gupid/Spacemouse_DIY_project/Spacemouse_develop/3Dmouse_keyboard/Profile/hid_composite_service.c

/********************************** (C) COPYRIGHT *******************************
 * File Name          : hidkbdservice.c
 * Author             : WCH
 * Version            : V1.0
 * Date               : 2018/12/10
 * Description        : 键盘服务
 *********************************************************************************
 * Copyright (c) 2021 Nanjing Qinheng Microelectronics Co., Ltd.
 * Attention: This software (modified or not) and binary are used for 
 * microcontroller manufactured by Nanjing Qinheng Microelectronics.
 *******************************************************************************/

/*********************************************************************
 * INCLUDES
 */
#include "CONFIG.h"
#include "hid_composite_service.h"
#include "hiddev.h"
#include "battservice.h"

/*********************************************************************
 * MACROS
 */

/*********************************************************************
 * CONSTANTS
 */

/*********************************************************************
 * TYPEDEFS
 */

/*********************************************************************
 * GLOBAL VARIABLES
 */
// HID service
const uint8_t hidServUUID[ATT_BT_UUID_SIZE] = {
    LO_UINT16(HID_SERV_UUID), HI_UINT16(HID_SERV_UUID)};

// HID Boot Keyboard Input Report characteristic
const uint8_t hidBootKeyInputUUID[ATT_BT_UUID_SIZE] = {
    LO_UINT16(BOOT_KEY_INPUT_UUID), HI_UINT16(BOOT_KEY_INPUT_UUID)};

// HID Boot Keyboard Output Report characteristic
const uint8_t hidBootKeyOutputUUID[ATT_BT_UUID_SIZE] = {
    LO_UINT16(BOOT_KEY_OUTPUT_UUID), HI_UINT16(BOOT_KEY_OUTPUT_UUID)};

// HID Information characteristic
const uint8_t hidInfoUUID[ATT_BT_UUID_SIZE] = {
    LO_UINT16(HID_INFORMATION_UUID), HI_UINT16(HID_INFORMATION_UUID)};

// HID Report Map characteristic
const uint8_t hidReportMapUUID[ATT_BT_UUID_SIZE] = {
    LO_UINT16(REPORT_MAP_UUID), HI_UINT16(REPORT_MAP_UUID)};

// HID Control Point characteristic
const uint8_t hidControlPointUUID[ATT_BT_UUID_SIZE] = {
    LO_UINT16(HID_CTRL_PT_UUID), HI_UINT16(HID_CTRL_PT_UUID)};

// HID Report characteristic
const uint8_t hidReportUUID[ATT_BT_UUID_SIZE] = {
    LO_UINT16(REPORT_UUID), HI_UINT16(REPORT_UUID)};

// HID Protocol Mode characteristic
const uint8_t hidProtocolModeUUID[ATT_BT_UUID_SIZE] = {
    LO_UINT16(PROTOCOL_MODE_UUID), HI_UINT16(PROTOCOL_MODE_UUID)};

/*********************************************************************
 * EXTERNAL VARIABLES
 */

/*********************************************************************
 * EXTERNAL FUNCTIONS
 */

/*********************************************************************
 * LOCAL VARIABLES
 */

// HID Information characteristic value
static const uint8_t hidInfo[HID_INFORMATION_LEN] = {
    LO_UINT16(0x0111), HI_UINT16(0x0111), // bcdHID (USB HID version)
    0x00,                                 // bCountryCode
    HID_FEATURE_FLAGS                     // Flags
};

// hid_composite_service.c

// HID Report Map characteristic value (Corrected and Aligned with USB Version)
static const uint8_t hidReportMap[] = {
    // --- TLC 1: SpaceMouse ---
    0x05, 0x01,       // Usage Page (Generic Desktop)
    0x09, 0x08,       // Usage (Multi-Axis Controller)
    0xA1, 0x01,       // Collection (Application)
        // 报告ID 1: 平移
        0x85, 0x01,       //   Report ID (1)
        0x09, 0x30,       //   Usage (X)
        0x09, 0x31,       //   Usage (Y)
        0x09, 0x32,       //   Usage (Z)
        0x16, 0xA2, 0xFE, //   Logical Minimum (-350)
        0x26, 0x5E, 0x01, //   Logical Maximum (350)
        0x75, 0x10,       //   Report Size (16)
        0x95, 0x03,       //   Report Count (3)
        0x81, 0x02,       //   Input (Data, Var, Abs)
        // 报告ID 2: 旋转
        0x85, 0x02,       //   Report ID (2)
        0x09, 0x33,       //   Usage (Rx)
        0x09, 0x34,       //   Usage (Ry)
        0x09, 0x35,       //   Usage (Rz)
        0x16, 0xA2, 0xFE, //   Logical Minimum (-350)
        0x26, 0x5E, 0x01, //   Logical Maximum (350)
        0x75, 0x10,       //   Report Size (16)
        0x95, 0x03,       //   Report Count (3)
        0x81, 0x02,       //   Input (Data, Var, Abs)
        // 报告ID 3: 按键
        0x85, 0x03,       //   Report ID (3)
        0x05, 0x09,       //   Usage Page (Button)
        0x19, 0x01,       //   Usage Minimum (Button 1)
        0x29, 0x20,       //   Usage Maximum (Button 32)
        0x15, 0x00,       //   Logical Minimum (0)
        0x25, 0x01,       //   Logical Maximum (1)
        0x75, 0x01,       //   Report Size (1)
        0x95, 0x20,       //   Report Count (32)
        0x81, 0x02,       //   Input (Data, Var, Abs)
        // 报告ID 4: LED
        0x85, 0x04,       //   Report ID (4)
        0x05, 0x08,       //   Usage Page (LEDs)
        0x09, 0x4B,       //   Usage (Generic Indicator)
        0x15, 0x00,       //   Logical Minimum (0)
        0x25, 0x01,       //   Logical Maximum (1)
        0x75, 0x01,       //   Report Size (1)
        0x95, 0x01,       //   Report Count (1)
        0x91, 0x02,       //   Output (Data, Var, Abs)
        0x75, 0x07,       //   Report Size (7) - Padding
        0x95, 0x01,       //   Report Count (1)
        0x91, 0x03,       //   Output (Constant)
    0xC0,             // End Collection (SpaceMouse)

    // --- TLC 2: Keyboard ---
    0x05, 0x01,       // Usage Page (Generic Desktop)
    0x09, 0x06,       // Usage (Keyboard)
    0xA1, 0x01,       // Collection (Application)
        // 报告ID 5: 键盘输入/输出
        0x85, 0x05,       //   Report ID (5)
        // Modifier keys (Input)
        0x05, 0x07,       //   Usage Page (Key Codes)
        0x19, 0xE0,       //   Usage Minimum (LeftControl)
        0x29, 0xE7,       //   Usage Maximum (RightGUI)
        0x15, 0x00,       //   Logical Minimum (0)
        0x25, 0x01,       //   Logical Maximum (1)
        0x75, 0x01,       //   Report Size (1)
        0x95, 0x08,       //   Report Count (8)
        0x81, 0x02,       //   Input (Data, Var, Abs)
        // Reserved byte (Input)
        0x95, 0x01,       //   Report Count (1)
        0x75, 0x08,       //   Report Size (8)
        0x81, 0x01,       //   Input (Constant)
        // Key array (Input)
        0x95, 0x06,       //   Report Count (6)
        0x75, 0x08,       //   Report Size (8)
        0x15, 0x00,       //   Logical Minimum (0)
        0x25, 0x65,       //   Logical Maximum (101)
        0x05, 0x07,       //   Usage Page (Key Codes)
        0x19, 0x00,       //   Usage Minimum (Reserved)
        0x29, 0x65,       //   Usage Maximum (Keyboard Application)
        0x81, 0x00,       //   Input (Data, Array)
        // LED (Output)
        0x05, 0x08,       //   Usage Page (LEDs)
        0x19, 0x01,       //   Usage Minimum (Num Lock)
        0x29, 0x05,       //   Usage Maximum (Kana)
        0x95, 0x05,       //   Report Count (5)
        0x75, 0x01,       //   Report Size (1)
        0x91, 0x02,       //   Output (Data, Var, Abs)
        // LED padding (Output)
        0x95, 0x01,       //   Report Count (1)
        0x75, 0x03,       //   Report Size (3)
        0x91, 0x03,       //   Output (Constant)
    0xC0,             // End Collection (Keyboard)

    // --- TLC 3: Feature Report (可以保持独立或合并) ---
    // 这个报告比较特殊，可以单独存在
    0x05, 0x01,       // Usage Page (Generic Desktop)
    0x09, 0x00,       // Usage (Undefined)
    0xA1, 0x01,       // Collection (Application)
        // 报告ID 6: Feature 报告
        0x85, 0x06,       // Report ID (6)
        0x09, 0x01,       // Usage (Pointer)
        0x15, 0x00,       // Logical Minimum (0)
        0x26, 0xFF, 0x00, // Logical Maximum (255)
        0x75, 0x08,       // Report Size (8)
        0x95, 0x01,       // Report Count (1)
        0xB1, 0x02,       // Feature (Data,Var,Abs)
    0xC0              // End Collection
};

// HID report map length
uint16_t hidReportMapLen = sizeof(hidReportMap);

// HID report mapping table
static hidRptMap_t hidRptMap[HID_NUM_REPORTS];

/*********************************************************************
 * Profile Attributes - variables
 */

// HID Service attribute
static const gattAttrType_t hidService = {ATT_BT_UUID_SIZE, hidServUUID};

// Include attribute (Battery service)
static uint16_t include = GATT_INVALID_HANDLE;

// HID Information characteristic
static uint8_t hidInfoProps = GATT_PROP_READ;

// HID Report Map characteristic
static uint8_t hidReportMapProps = GATT_PROP_READ;

// HID External Report Reference Descriptor
static uint8_t hidExtReportRefDesc[ATT_BT_UUID_SIZE] =
    {LO_UINT16(BATT_LEVEL_UUID), HI_UINT16(BATT_LEVEL_UUID)};

// HID Control Point characteristic
static uint8_t hidControlPointProps = GATT_PROP_WRITE_NO_RSP;
static uint8_t hidControlPoint;

// HID Protocol Mode characteristic
static uint8_t hidProtocolModeProps = GATT_PROP_READ | GATT_PROP_WRITE_NO_RSP;
uint8_t        hidProtocolMode = HID_PROTOCOL_MODE_REPORT;

// HID Report characteristic, key input
static uint8_t       hidReportKeyInProps = GATT_PROP_READ | GATT_PROP_NOTIFY;
static uint8_t       hidReportKeyIn;
static gattCharCfg_t hidReportKeyInClientCharCfg[GATT_MAX_NUM_CONN];

// HID Report Reference characteristic descriptor, key input
static uint8_t hidReportRefKeyIn[HID_REPORT_REF_LEN] =
    {HID_RPT_ID_KEY_IN, HID_REPORT_TYPE_INPUT};

// HID Report characteristic, LED output
static uint8_t hidReportLedOutProps = GATT_PROP_READ | GATT_PROP_WRITE | GATT_PROP_WRITE_NO_RSP;
static uint8_t hidReportLedOut;

// HID Report Reference characteristic descriptor, LED output
static uint8_t hidReportRefLedOut[HID_REPORT_REF_LEN] =
    {HID_RPT_ID_LED_OUT, HID_REPORT_TYPE_OUTPUT};

// HID Boot Keyboard Input Report
static uint8_t       hidReportBootKeyInProps = GATT_PROP_READ | GATT_PROP_NOTIFY;
static uint8_t       hidReportBootKeyIn;
static gattCharCfg_t hidReportBootKeyInClientCharCfg[GATT_MAX_NUM_CONN];

// HID Boot Keyboard Output Report
static uint8_t hidReportBootKeyOutProps = GATT_PROP_READ | GATT_PROP_WRITE | GATT_PROP_WRITE_NO_RSP;
static uint8_t hidReportBootKeyOut;

// Feature Report
static uint8_t hidReportFeatureProps = GATT_PROP_READ | GATT_PROP_WRITE;
static uint8_t hidReportFeature;

// HID Report Reference characteristic descriptor, Feature
static uint8_t hidReportRefFeature[HID_REPORT_REF_LEN] =
    {HID_RPT_ID_FEATURE, HID_REPORT_TYPE_FEATURE};

// ---SpaceMouse平移报告 (ID: 2)---
static uint8_t       hidReportSpaceTransInProps = GATT_PROP_READ | GATT_PROP_NOTIFY;
static uint8_t       hidReportSpaceTransIn;
static gattCharCfg_t hidReportSpaceTransInClientCharCfg[GATT_MAX_NUM_CONN];
// 定义平移报告ID为2，类型为输入
static uint8_t hidReportRefSpaceTransIn[HID_REPORT_REF_LEN] = { HID_RPT_ID_SPACE_TRANS_IN, HID_REPORT_TYPE_INPUT };

// ---SpaceMouse旋转报告 (ID: 3)---
static uint8_t       hidReportSpaceRotInProps = GATT_PROP_READ | GATT_PROP_NOTIFY;
static uint8_t       hidReportSpaceRotIn;
static gattCharCfg_t hidReportSpaceRotInClientCharCfg[GATT_MAX_NUM_CONN];
// 定义旋转报告ID为3，类型为输入
static uint8_t hidReportRefSpaceRotIn[HID_REPORT_REF_LEN] = { HID_RPT_ID_SPACE_ROT_IN, HID_REPORT_TYPE_INPUT };

// --- SpaceMouse按键报告 (ID: 4) ---
static uint8_t       hidReportSpaceBtnInProps = GATT_PROP_READ | GATT_PROP_NOTIFY;
static uint8_t       hidReportSpaceBtnIn;
static gattCharCfg_t hidReportSpaceBtnInClientCharCfg[GATT_MAX_NUM_CONN];
// 定义按键报告ID为4，类型为输入
static uint8_t hidReportRefSpaceBtnIn[HID_REPORT_REF_LEN] = { HID_RPT_ID_SPACE_BTN_IN, HID_REPORT_TYPE_INPUT };

// --- SpaceMouse LED输出报告 (ID: 5) ---
static uint8_t hidReportSpaceLedOutProps = GATT_PROP_READ | GATT_PROP_WRITE | GATT_PROP_WRITE_NO_RSP;
static uint8_t hidReportSpaceLedOut;
// 定义LED报告ID为5，类型为输出
static uint8_t hidReportRefSpaceLedOut[HID_REPORT_REF_LEN] = { HID_RPT_ID_SPACE_LED_OUT, HID_REPORT_TYPE_OUTPUT };
/*********************************************************************
 * Profile Attributes - Table
 */

static gattAttribute_t hidAttrTbl[] = {
    // HID Service
    {
        {ATT_BT_UUID_SIZE, primaryServiceUUID}, /* type */
        GATT_PERMIT_READ,                       /* permissions */
        0,                                      /* handle */
        (uint8_t *)&hidService                  /* pValue */
    },

    // Included service (battery)
    {
        {ATT_BT_UUID_SIZE, includeUUID},
        GATT_PERMIT_READ,
        0,
        (uint8_t *)&include},

    // HID Information characteristic declaration
    {
        {ATT_BT_UUID_SIZE, characterUUID},
        GATT_PERMIT_READ,
        0,
        &hidInfoProps},

    // HID Information characteristic
    {
        {ATT_BT_UUID_SIZE, hidInfoUUID},
        GATT_PERMIT_ENCRYPT_READ,
        0,
        (uint8_t *)hidInfo},

    // HID Control Point characteristic declaration
    {
        {ATT_BT_UUID_SIZE, characterUUID},
        GATT_PERMIT_READ,
        0,
        &hidControlPointProps},

    // HID Control Point characteristic
    {
        {ATT_BT_UUID_SIZE, hidControlPointUUID},
        GATT_PERMIT_ENCRYPT_WRITE,
        0,
        &hidControlPoint},

    // HID Protocol Mode characteristic declaration
    {
        {ATT_BT_UUID_SIZE, characterUUID},
        GATT_PERMIT_READ,
        0,
        &hidProtocolModeProps},

    // HID Protocol Mode characteristic
    {
        {ATT_BT_UUID_SIZE, hidProtocolModeUUID},
        GATT_PERMIT_ENCRYPT_READ | GATT_PERMIT_ENCRYPT_WRITE,
        0,
        &hidProtocolMode},

    // HID Report Map characteristic declaration
    {
        {ATT_BT_UUID_SIZE, characterUUID},
        GATT_PERMIT_READ,
        0,
        &hidReportMapProps},

    // HID Report Map characteristic
    {
        {ATT_BT_UUID_SIZE, hidReportMapUUID},
        GATT_PERMIT_ENCRYPT_READ,
        0,
        (uint8_t *)hidReportMap},

    // HID External Report Reference Descriptor
    {
        {ATT_BT_UUID_SIZE, extReportRefUUID},
        GATT_PERMIT_READ,
        0,
        hidExtReportRefDesc

    },

    // HID Report characteristic, key input declaration
    {
        {ATT_BT_UUID_SIZE, characterUUID},
        GATT_PERMIT_READ,
        0,
        &hidReportKeyInProps},

    // HID Report characteristic, key input
    {
        {ATT_BT_UUID_SIZE, hidReportUUID},
        GATT_PERMIT_ENCRYPT_READ,
        0,
        &hidReportKeyIn},

    // HID Report characteristic client characteristic configuration
    {
        {ATT_BT_UUID_SIZE, clientCharCfgUUID},
        GATT_PERMIT_READ | GATT_PERMIT_ENCRYPT_WRITE,
        0,
        (uint8_t *)&hidReportKeyInClientCharCfg},

    // HID Report Reference characteristic descriptor, key input
    {
        {ATT_BT_UUID_SIZE, reportRefUUID},
        GATT_PERMIT_READ,
        0,
        hidReportRefKeyIn},

    // HID Report characteristic, LED output declaration
    {
        {ATT_BT_UUID_SIZE, characterUUID},
        GATT_PERMIT_READ,
        0,
        &hidReportLedOutProps},

    // HID Report characteristic, LED output
    {
        {ATT_BT_UUID_SIZE, hidReportUUID},
        GATT_PERMIT_ENCRYPT_READ | GATT_PERMIT_ENCRYPT_WRITE,
        0,
        &hidReportLedOut},
        
    // HID Report Reference characteristic descriptor, LED output
    {
        {ATT_BT_UUID_SIZE, reportRefUUID},
        GATT_PERMIT_READ,
        0,
        hidReportRefLedOut
    },

    // --- HID Report characteristic, SpaceMouse translation input declaration ---
    {
        {ATT_BT_UUID_SIZE, characterUUID},
        GATT_PERMIT_READ,
        0,
        &hidReportSpaceTransInProps
    },

    // --- HID Report characteristic, SpaceMouse translation input ---
    {
        {ATT_BT_UUID_SIZE, hidReportUUID},
        GATT_PERMIT_ENCRYPT_READ,
        0,
        &hidReportSpaceTransIn
    },

    // --- HID Report characteristic client characteristic configuration (CCCD) ---
    {
        {ATT_BT_UUID_SIZE, clientCharCfgUUID},
        GATT_PERMIT_READ | GATT_PERMIT_ENCRYPT_WRITE,
        0,
        (uint8_t *)&hidReportSpaceTransInClientCharCfg
    },

    // --- HID Report Reference characteristic descriptor, SpaceMouse translation input ---
    {
        {ATT_BT_UUID_SIZE, reportRefUUID},
        GATT_PERMIT_READ,
        0,
        hidReportRefSpaceTransIn
    },

    // --- HID Report characteristic, SpaceMouse rotation input declaration ---
    {
        {ATT_BT_UUID_SIZE, characterUUID},
        GATT_PERMIT_READ,
        0,
        &hidReportSpaceRotInProps
    },

    // --- HID Report characteristic, SpaceMouse rotation input ---
    {
        {ATT_BT_UUID_SIZE, hidReportUUID},
        GATT_PERMIT_ENCRYPT_READ,
        0,
        &hidReportSpaceRotIn
    },

    // --- HID Report characteristic client characteristic configuration (CCCD) ---
    {
        {ATT_BT_UUID_SIZE, clientCharCfgUUID},
        GATT_PERMIT_READ | GATT_PERMIT_ENCRYPT_WRITE,
        0,
        (uint8_t *)&hidReportSpaceRotInClientCharCfg
    },

    // --- HID Report Reference characteristic descriptor, SpaceMouse rotation input ---
    {
        {ATT_BT_UUID_SIZE, reportRefUUID},
        GATT_PERMIT_READ,
        0,
        hidReportRefSpaceRotIn
    },

    // --- [!!] 新增：HID Report characteristic, SpaceMouse button input declaration ---
    {
        {ATT_BT_UUID_SIZE, characterUUID},
        GATT_PERMIT_READ,
        0,
        &hidReportSpaceBtnInProps
    },

    // --- [!!] 新增：HID Report characteristic, SpaceMouse button input ---
    {
        {ATT_BT_UUID_SIZE, hidReportUUID}, // 使用通用报告UUID
        GATT_PERMIT_ENCRYPT_READ,
        0,
        &hidReportSpaceBtnIn
    },

    // --- [!!] 新增：HID Report characteristic client characteristic configuration (CCCD) ---
    {
        {ATT_BT_UUID_SIZE, clientCharCfgUUID},
        GATT_PERMIT_READ | GATT_PERMIT_ENCRYPT_WRITE,
        0,
        (uint8_t *)&hidReportSpaceBtnInClientCharCfg
    },

    // --- [!!] 新增：HID Report Reference characteristic descriptor, SpaceMouse button input ---
    {
        {ATT_BT_UUID_SIZE, reportRefUUID},
        GATT_PERMIT_READ,
        0,
        hidReportRefSpaceBtnIn
    },

    // --- [!!] 新增：HID Report characteristic, SpaceMouse LED output declaration ---
    {
        {ATT_BT_UUID_SIZE, characterUUID},
        GATT_PERMIT_READ,
        0,
        &hidReportSpaceLedOutProps
    },

    // --- [!!] 新增：HID Report characteristic, SpaceMouse LED output ---
    {
        {ATT_BT_UUID_SIZE, hidReportUUID}, // 使用通用报告UUID
        GATT_PERMIT_ENCRYPT_READ | GATT_PERMIT_ENCRYPT_WRITE,
        0,
        &hidReportSpaceLedOut
    },
        
    // --- [!!] 新增：HID Report Reference characteristic descriptor, SpaceMouse LED output ---
    {
        {ATT_BT_UUID_SIZE, reportRefUUID},
        GATT_PERMIT_READ,
        0,
        hidReportRefSpaceLedOut
    },
    
    // HID Boot Keyboard Input Report declaration
    {
        {ATT_BT_UUID_SIZE, characterUUID},
        GATT_PERMIT_READ,
        0,
        &hidReportBootKeyInProps},

    // HID Boot Keyboard Input Report
    {
        {ATT_BT_UUID_SIZE, hidBootKeyInputUUID},
        GATT_PERMIT_ENCRYPT_READ,
        0,
        &hidReportBootKeyIn},

    // HID Boot Keyboard Input Report characteristic client characteristic configuration
    {
        {ATT_BT_UUID_SIZE, clientCharCfgUUID},
        GATT_PERMIT_READ | GATT_PERMIT_ENCRYPT_WRITE,
        0,
        (uint8_t *)&hidReportBootKeyInClientCharCfg},

    // HID Boot Keyboard Output Report declaration
    {
        {ATT_BT_UUID_SIZE, characterUUID},
        GATT_PERMIT_READ,
        0,
        &hidReportBootKeyOutProps},

    // HID Boot Keyboard Output Report
    {
        {ATT_BT_UUID_SIZE, hidBootKeyOutputUUID},
        GATT_PERMIT_ENCRYPT_READ | GATT_PERMIT_ENCRYPT_WRITE,
        0,
        &hidReportBootKeyOut},

    // Feature Report declaration
    {
        {ATT_BT_UUID_SIZE, characterUUID},
        GATT_PERMIT_READ,
        0,
        &hidReportFeatureProps},

    // Feature Report
    {
        {ATT_BT_UUID_SIZE, hidReportUUID},
        GATT_PERMIT_ENCRYPT_READ | GATT_PERMIT_ENCRYPT_WRITE,
        0,
        &hidReportFeature},

    // HID Report Reference characteristic descriptor, feature
    {
        {ATT_BT_UUID_SIZE, reportRefUUID},
        GATT_PERMIT_READ,
        0,
        hidReportRefFeature},
};

// Attribute index enumeration-- these indexes match array elements above
enum
{
    HID_SERVICE_IDX,
    HID_INCLUDED_SERVICE_IDX,
    HID_INFO_DECL_IDX,
    HID_INFO_IDX,
    HID_CONTROL_POINT_DECL_IDX,
    HID_CONTROL_POINT_IDX,
    HID_PROTOCOL_MODE_DECL_IDX,
    HID_PROTOCOL_MODE_IDX,
    HID_REPORT_MAP_DECL_IDX,
    HID_REPORT_MAP_IDX,
    HID_EXT_REPORT_REF_DESC_IDX,

    // --- 键盘相关 ---
    HID_REPORT_KEY_IN_DECL_IDX,
    HID_REPORT_KEY_IN_IDX,
    HID_REPORT_KEY_IN_CCCD_IDX,
    HID_REPORT_REF_KEY_IN_IDX,
    HID_REPORT_LED_OUT_DECL_IDX,
    HID_REPORT_LED_OUT_IDX,
    HID_REPORT_REF_LED_OUT_IDX,

    // --- spacemouse相关 ----
    HID_REPORT_SPACETRANS_IN_DECL_IDX,
    HID_REPORT_SPACETRANS_IN_IDX,
    HID_REPORT_SPACETRANS_IN_CCCD_IDX,
    HID_REPORT_REF_SPACETRANS_IN_IDX,
    HID_REPORT_SPACEROT_IN_DECL_IDX,
    HID_REPORT_SPACEROT_IN_IDX,
    HID_REPORT_SPACEROT_IN_CCCD_IDX,
    HID_REPORT_REF_SPACEROT_IN_IDX,
    // --- [!!] 新增：SpaceMouse按键和LED的索引 ---
    HID_REPORT_SPACEBTN_IN_DECL_IDX,
    HID_REPORT_SPACEBTN_IN_IDX,
    HID_REPORT_SPACEBTN_IN_CCCD_IDX,
    HID_REPORT_REF_SPACEBTN_IN_IDX,
    HID_REPORT_SPACELED_OUT_DECL_IDX,
    HID_REPORT_SPACELED_OUT_IDX,
    HID_REPORT_REF_SPACELED_OUT_IDX,

    // --- 启动模式相关 ---
    HID_BOOT_KEY_IN_DECL_IDX,
    HID_BOOT_KEY_IN_IDX,
    HID_BOOT_KEY_IN_CCCD_IDX,
    HID_BOOT_KEY_OUT_DECL_IDX,
    HID_BOOT_KEY_OUT_IDX,

    // --- Feature报告 ---
    HID_FEATURE_DECL_IDX,
    HID_FEATURE_IDX,
    HID_REPORT_REF_FEATURE_IDX
};

/*********************************************************************
 * LOCAL FUNCTIONS
 */

/*********************************************************************
 * PROFILE CALLBACKS
 */

// Service Callbacks
gattServiceCBs_t hidKbdCBs = {
    HidDev_ReadAttrCB,  // Read callback function pointer
    HidDev_WriteAttrCB, // Write callback function pointer
    NULL                // Authorization callback function pointer
};

/*********************************************************************
 * PUBLIC FUNCTIONS
 */

/*********************************************************************
 * @fn      HidComposite_AddService
 *
 * @brief   Initializes the HID Composite Service by registering
 * GATT attributes with the GATT server.
 *
 * @return  Success or Failure
 */
bStatus_t HidComposite_AddService(void)
{
    uint8_t status = SUCCESS;

    // 1. 初始化客户端特性配置 (Client Characteristic Configuration)
    //    [!!] 新增SpaceMouse按键的CCCD初始化
    GATTServApp_InitCharCfg(INVALID_CONNHANDLE, hidReportKeyInClientCharCfg);
    GATTServApp_InitCharCfg(INVALID_CONNHANDLE, hidReportBootKeyInClientCharCfg);
    GATTServApp_InitCharCfg(INVALID_CONNHANDLE, hidReportSpaceTransInClientCharCfg);
    GATTServApp_InitCharCfg(INVALID_CONNHANDLE, hidReportSpaceRotInClientCharCfg);
    GATTServApp_InitCharCfg(INVALID_CONNHANDLE, hidReportSpaceBtnInClientCharCfg); // <-- 新增

    // 2. 注册GATT属性表
    status = GATTServApp_RegisterService(hidAttrTbl, GATT_NUM_ATTRS(hidAttrTbl), GATT_MAX_ENCRYPT_KEY_SIZE, &hidKbdCBs);
    if(status != SUCCESS)
    {
        return status;
    }

    // 3. 设置包含的电池服务 (保持不变)
    Batt_GetParameter(BATT_PARAM_SERVICE_HANDLE,
                      &GATT_INCLUDED_HANDLE(hidAttrTbl, HID_INCLUDED_SERVICE_IDX));

    // 4. --- 核心修正：重建报告ID和GATT句柄的映射表 ---
    //    总报告数现在是10个
    
    // 报告 0-5 (保持不变)
    // ... (键盘、LED、启动模式、Feature、电池) ...
    hidRptMap[0].id = hidReportRefKeyIn[0];
    hidRptMap[0].type = hidReportRefKeyIn[1];
    hidRptMap[0].handle = hidAttrTbl[HID_REPORT_KEY_IN_IDX].handle;
    hidRptMap[0].cccdHandle = hidAttrTbl[HID_REPORT_KEY_IN_CCCD_IDX].handle;
    hidRptMap[0].mode = HID_PROTOCOL_MODE_REPORT;

    hidRptMap[1].id = hidReportRefLedOut[0];
    hidRptMap[1].type = hidReportRefLedOut[1];
    hidRptMap[1].handle = hidAttrTbl[HID_REPORT_LED_OUT_IDX].handle;
    hidRptMap[1].cccdHandle = 0;
    hidRptMap[1].mode = HID_PROTOCOL_MODE_REPORT;

    hidRptMap[2].id = hidReportRefKeyIn[0];
    hidRptMap[2].type = hidReportRefKeyIn[1];
    hidRptMap[2].handle = hidAttrTbl[HID_BOOT_KEY_IN_IDX].handle;
    hidRptMap[2].cccdHandle = hidAttrTbl[HID_BOOT_KEY_IN_CCCD_IDX].handle;
    hidRptMap[2].mode = HID_PROTOCOL_MODE_BOOT;

    hidRptMap[3].id = hidReportRefLedOut[0];
    hidRptMap[3].type = hidReportRefLedOut[1];
    hidRptMap[3].handle = hidAttrTbl[HID_BOOT_KEY_OUT_IDX].handle;
    hidRptMap[3].cccdHandle = 0;
    hidRptMap[3].mode = HID_PROTOCOL_MODE_BOOT;

    hidRptMap[4].id = hidReportRefFeature[0];
    hidRptMap[4].type = hidReportRefFeature[1];
    hidRptMap[4].handle = hidAttrTbl[HID_FEATURE_IDX].handle;
    hidRptMap[4].cccdHandle = 0;
    hidRptMap[4].mode = HID_PROTOCOL_MODE_REPORT;

    Batt_GetParameter(BATT_PARAM_BATT_LEVEL_IN_REPORT, &(hidRptMap[5]));

    // 报告 6: SpaceMouse 平移报告 (Report ID: 2)
    hidRptMap[6].id = hidReportRefSpaceTransIn[0];
    hidRptMap[6].type = hidReportRefSpaceTransIn[1];
    hidRptMap[6].handle = hidAttrTbl[HID_REPORT_SPACETRANS_IN_IDX].handle;
    hidRptMap[6].cccdHandle = hidAttrTbl[HID_REPORT_SPACETRANS_IN_CCCD_IDX].handle;
    hidRptMap[6].mode = HID_PROTOCOL_MODE_REPORT;

    // 报告 7: SpaceMouse 旋转报告 (Report ID: 3)
    hidRptMap[7].id = hidReportRefSpaceRotIn[0];
    hidRptMap[7].type = hidReportRefSpaceRotIn[1];
    hidRptMap[7].handle = hidAttrTbl[HID_REPORT_SPACEROT_IN_IDX].handle;
    hidRptMap[7].cccdHandle = hidAttrTbl[HID_REPORT_SPACEROT_IN_CCCD_IDX].handle;
    hidRptMap[7].mode = HID_PROTOCOL_MODE_REPORT;

    // --- [!!] 新增：注册SpaceMouse按键和LED报告的映射 ---
    // 报告 8: SpaceMouse 按键报告 (Report ID: 4)
    hidRptMap[8].id = hidReportRefSpaceBtnIn[0];
    hidRptMap[8].type = hidReportRefSpaceBtnIn[1];
    hidRptMap[8].handle = hidAttrTbl[HID_REPORT_SPACEBTN_IN_IDX].handle;
    hidRptMap[8].cccdHandle = hidAttrTbl[HID_REPORT_SPACEBTN_IN_CCCD_IDX].handle;
    hidRptMap[8].mode = HID_PROTOCOL_MODE_REPORT;

    // 报告 9: SpaceMouse LED 输出报告 (Report ID: 5)
    hidRptMap[9].id = hidReportRefSpaceLedOut[0];
    hidRptMap[9].type = hidReportRefSpaceLedOut[1];
    hidRptMap[9].handle = hidAttrTbl[HID_REPORT_SPACELED_OUT_IDX].handle;
    hidRptMap[9].cccdHandle = 0; // 输出报告没有CCCD
    hidRptMap[9].mode = HID_PROTOCOL_MODE_REPORT;

    // 5. 注册所有报告 ([!!] 数量改为HID_NUM_REPORTS)
    HidDev_RegisterReports(HID_NUM_REPORTS, hidRptMap);

    return (status);
}
/*********************************************************************
 * @fn      Hid_SetParameter
 *
 * @brief   Set a HID Kbd parameter.
 *
 * @param   id - HID report ID.
 * @param   type - HID report type.
 * @param   uuid - attribute uuid.
 * @param   len - length of data to right.
 * @param   pValue - pointer to data to write.  This is dependent on
 *          the input parameters and WILL be cast to the appropriate
 *          data type (example: data type of uint16_t will be cast to
 *          uint16_t pointer).
 *
 * @return  GATT status code.
 */
uint8_t Hid_SetParameter(uint8_t id, uint8_t type, uint16_t uuid, uint8_t len, void *pValue)
{
    bStatus_t ret = SUCCESS;

    switch(uuid)
    {
        case REPORT_UUID:
            if(type == HID_REPORT_TYPE_OUTPUT)
            {
                if(len == 1)
                {
                    hidReportLedOut = *((uint8_t *)pValue);
                }
                else
                {
                    ret = ATT_ERR_INVALID_VALUE_SIZE;
                }
            }
            else if(type == HID_REPORT_TYPE_FEATURE)
            {
                if(len == 1)
                {
                    hidReportFeature = *((uint8_t *)pValue);
                }
                else
                {
                    ret = ATT_ERR_INVALID_VALUE_SIZE;
                }
            }
            else
            {
                ret = ATT_ERR_ATTR_NOT_FOUND;
            }
            break;

        case BOOT_KEY_OUTPUT_UUID:
            if(len == 1)
            {
                hidReportBootKeyOut = *((uint8_t *)pValue);
            }
            else
            {
                ret = ATT_ERR_INVALID_VALUE_SIZE;
            }
            break;

        default:
            // ignore the request
            break;
    }

    return (ret);
}

/*********************************************************************
 * @fn      Hid_GetParameter
 *
 * @brief   Get a HID Kbd parameter.
 *
 * @param   id - HID report ID.
 * @param   type - HID report type.
 * @param   uuid - attribute uuid.
 * @param   pLen - length of data to be read
 * @param   pValue - pointer to data to get.  This is dependent on
 *          the input parameters and WILL be cast to the appropriate
 *          data type (example: data type of uint16_t will be cast to
 *          uint16_t pointer).
 *
 * @return  GATT status code.
 */
uint8_t Hid_GetParameter(uint8_t id, uint8_t type, uint16_t uuid, uint16_t *pLen, void *pValue)
{
    switch(uuid)
    {
        case REPORT_UUID:
            if(type == HID_REPORT_TYPE_OUTPUT)
            {
                *((uint8_t *)pValue) = hidReportLedOut;
                *pLen = 1;
            }
            else if(type == HID_REPORT_TYPE_FEATURE)
            {
                *((uint8_t *)pValue) = hidReportFeature;
                *pLen = 1;
            }
            else
            {
                *pLen = 0;
            }
            break;

        case BOOT_KEY_OUTPUT_UUID:
            *((uint8_t *)pValue) = hidReportBootKeyOut;
            *pLen = 1;
            break;

        default:
            *pLen = 0;
            break;
    }

    return (SUCCESS);
}

/*********************************************************************
*********************************************************************/
