gupid/Spacemouse_DIY_project/Spacemouse_develop/3Dmouse_keyboard/WA_Library_V6.0/WA_GPIO/GPIO_IT.c

#include "GPIO_IT.h"
#include "UART.h"
/* GPIOA外部中断服务函数 */
__INTERRUPT
__HIGH_CODE
void GPIOA_IRQHandler(void)
{
    WA_GPIOA_IQRHandler();
}


/* GPIOB外部中断服务函数 */
__INTERRUPT
__HIGH_CODE
void GPIOB_IRQHandler(void)
{
    WA_GPIOB_IQRHandler();   
}

//中断服务分配函数
void WA_GPIOA_IQRHandler(void)
{
    if(GPIOA_ReadITFlagBit(GPIO_Pin_0))
    {
        GPIOA_ClearITFlagBit(GPIO_Pin_0);
        WA_GPIOA_EventCallBack(GPIO_Pin_0);
    }

    if(GPIOA_ReadITFlagBit(GPIO_Pin_1))
    {
        GPIOA_ClearITFlagBit(GPIO_Pin_1);
        WA_GPIOA_EventCallBack(GPIO_Pin_1);
    }

    if(GPIOA_ReadITFlagBit(GPIO_Pin_2))
    {
        GPIOA_ClearITFlagBit(GPIO_Pin_2);
        WA_GPIOA_EventCallBack(GPIO_Pin_2);
    }

    if(GPIOA_ReadITFlagBit(GPIO_Pin_3))
    {
        GPIOA_ClearITFlagBit(GPIO_Pin_3);
        WA_GPIOA_EventCallBack(GPIO_Pin_3);
    }

    if(GPIOA_ReadITFlagBit(GPIO_Pin_4))
    {
        GPIOA_ClearITFlagBit(GPIO_Pin_4);
        WA_GPIOA_EventCallBack(GPIO_Pin_4);
    }

    if(GPIOA_ReadITFlagBit(GPIO_Pin_5))
    {
        GPIOA_ClearITFlagBit(GPIO_Pin_5);
        WA_GPIOA_EventCallBack(GPIO_Pin_5);
    }

    if(GPIOA_ReadITFlagBit(GPIO_Pin_6))
    {
        GPIOA_ClearITFlagBit(GPIO_Pin_6);
        WA_GPIOA_EventCallBack(GPIO_Pin_6);
    }

    if(GPIOA_ReadITFlagBit(GPIO_Pin_7))
    {
        GPIOA_ClearITFlagBit(GPIO_Pin_7);
        WA_GPIOA_EventCallBack(GPIO_Pin_7);
    }

    if(GPIOA_ReadITFlagBit(GPIO_Pin_8))
    {
        GPIOA_ClearITFlagBit(GPIO_Pin_8);
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
    }

    if(GPIOB_ReadITFlagBit(GPIO_Pin_14))
    {
        GPIOB_ClearITFlagBit(GPIO_Pin_14);
        WA_GPIOB_EventCallBack(GPIO_Pin_14);
    }

    if(GPIOB_ReadITFlagBit(GPIO_Pin_15))
    {
        GPIOB_ClearITFlagBit(GPIO_Pin_15);
        WA_GPIOB_EventCallBack(GPIO_Pin_15);
    }
}
