gupid/Spacemouse_DIY_project/Spacemouse_develop/3Dmouse_keyboard/WA_Library_V6.0/WA_TIME/TIM.c

/* 官方底层管脚映射有问题：TIM0的默认引脚是PA9，但是映射不到PB23，因为PB23默认做板载复位按键*/
/* 官方底层管脚映射有问题：TIM3的默认引脚是PB22，可以映射到PA2，他那个文件的注释是错的*/
#include "TIM.h"

/*  RB_PIN_TMR3   -  TMR3:  PA2 ->  PB22
 *  RB_PIN_TMR2   -  TMR2:  PA11 ->  PB11
 *  RB_PIN_TMR1   -  TMR1:  PA10 ->  PB10
 *  RB_PIN_TMR0   -  TMR0:  PA9 ->  PB23 */


//只有四个定时器资源，直接全定义了
TIM_HandleDef watime0;
TIM_HandleDef watime1;
TIM_HandleDef watime2;
TIM_HandleDef watime3;
//“厨子函数”
void WA_TIM_IT_MspInit(TIM_HandleDef *watime);


//初始化定时器||计数器
/* 
watime:地址
mode:模式   WA_TIMER    or  WA_COUNT
yingcshe:管脚映射使能
count_way：计数方式
count：计数值
*/
void WA_TIM_IT_Init(TIM_HandleDef *watime,uint16_t mode,uint8_t yingcshe,uint32_t fre,uint8_t count_way,uint32_t count)
{
    watime->Frequency = fre;
    watime->mode = mode;
    watime->count = count;
    watime->count_way = count_way;
    watime->print = yingcshe;
    //“厨子函数”
    WA_TIM_IT_MspInit(watime);
}

//“厨子函数”
void WA_TIM_IT_MspInit(TIM_HandleDef *watime)
{
    if(watime == &watime0)
    {
        if(watime->mode == WA_TIMER)
        {
            TMR0_TimerInit(FREQ_SYS  / watime->Frequency);         // 设置定时时间
            TMR0_ITCfg(ENABLE, TMR0_3_IT_CYC_END);                                  // 开启中断
            PFIC_EnableIRQ(TMR0_IRQn);
        }

        if(watime->mode == WA_COUNT)
        {
            if(watime->print == Pin_Enable)
            {
                GPIOB_ModeCfg(GPIO_Pin_23, GPIO_ModeIN_PD);
                GPIOPinRemap(ENABLE, RB_PIN_TMR0);
            }
            else 
            {
                GPIOA_ModeCfg(GPIO_Pin_9, GPIO_ModeIN_PD);
            }
            TMR0_EXTSingleCounterInit(watime->count_way);
            TMR0_CountOverflowCfg(watime->count); 
            /* 开启计数溢出中断，计慢1000个周期进入中断 */
            TMR0_ClearITFlag(TMR0_3_IT_CYC_END);
            PFIC_EnableIRQ(TMR0_IRQn);
            TMR0_ITCfg(ENABLE, TMR0_3_IT_CYC_END);
        }
        
    }

    if(watime == &watime1)
    {
        if(watime->mode == WA_TIMER)
        {
            TMR1_TimerInit(FREQ_SYS / watime->Frequency);         // 设置定时时间 100ms
            TMR1_ITCfg(ENABLE, TMR0_3_IT_CYC_END);                                  // 开启中断
            PFIC_EnableIRQ(TMR1_IRQn);
        }

        if(watime->mode == WA_COUNT)
        {
            if(watime->print == Pin_Enable)
            {
                GPIOB_ModeCfg(GPIO_Pin_10, GPIO_ModeIN_PD);
                GPIOPinRemap(ENABLE, RB_PIN_TMR1);
            }
            else 
            {
                GPIOA_ModeCfg(GPIO_Pin_10, GPIO_ModeIN_PD);
            }
            TMR1_EXTSingleCounterInit(watime->count_way);
            TMR1_CountOverflowCfg(watime->count); 
            /* 开启计数溢出中断，计慢1000个周期进入中断 */
            TMR1_ClearITFlag(TMR0_3_IT_CYC_END);
            PFIC_EnableIRQ(TMR1_IRQn);
            TMR1_ITCfg(ENABLE, TMR0_3_IT_CYC_END);
        }
     
    }

    if(watime == &watime2)
    {
        if(watime->mode == WA_TIMER)
        {
            TMR2_TimerInit(FREQ_SYS / watime->Frequency);         // 设置定时时间 100ms
            TMR2_ITCfg(ENABLE, TMR0_3_IT_CYC_END);                                  // 开启中断
            PFIC_EnableIRQ(TMR2_IRQn);
        }

        if(watime->mode == WA_COUNT)
        {
            if(watime->print == Pin_Enable)
            {
                GPIOB_ModeCfg(GPIO_Pin_11, GPIO_ModeIN_PD);
                GPIOPinRemap(ENABLE, RB_PIN_TMR2);
            }
            else 
            {
                GPIOA_ModeCfg(GPIO_Pin_11, GPIO_ModeIN_PD);
            }
            TMR2_EXTSingleCounterInit(watime->count_way);
            TMR2_CountOverflowCfg(watime->count); 
            /* 开启计数溢出中断，计慢1000个周期进入中断 */
            TMR2_ClearITFlag(TMR0_3_IT_CYC_END);
            PFIC_EnableIRQ(TMR2_IRQn);
            TMR2_ITCfg(ENABLE, TMR0_3_IT_CYC_END);
        }
    }

    if(watime == &watime3)
    {
        if(watime->mode == WA_TIMER)
        {
            TMR3_TimerInit(FREQ_SYS / watime->Frequency);         // 设置定时时间 100ms
            TMR3_ITCfg(ENABLE, TMR0_3_IT_CYC_END);                                  // 开启中断
            PFIC_EnableIRQ(TMR3_IRQn);
        }

        if(watime->mode == WA_COUNT)
        {
            if(watime->print == Pin_Enable)
            {
                GPIOA_ModeCfg(GPIO_Pin_2, GPIO_ModeIN_PD);
                GPIOPinRemap(ENABLE, RB_PIN_TMR3);
            }
            else 
            {
                GPIOB_ModeCfg(GPIO_Pin_22, GPIO_ModeIN_PD);
            }
            TMR3_EXTSingleCounterInit(watime->count_way);
            TMR3_CountOverflowCfg(watime->count); 
            /* 开启计数溢出中断，计慢1000个周期进入中断 */
            TMR3_ClearITFlag(TMR0_3_IT_CYC_END);
            PFIC_EnableIRQ(TMR3_IRQn);
            TMR3_ITCfg(ENABLE, TMR0_3_IT_CYC_END);
        }
        
    }
}


/* 定义周期中断的回调函数 */
__weak_symbol void WA_TIM_PeriodCallBack(TIM_HandleDef *watime)
{
    /* 开始你的程序 */
}

/* 定义计数中断的回调函数 */
__weak_symbol void WA_TIM_CountCallBack(TIM_HandleDef *watime)
{
    /* 开始你的程序 */
}
